bbs-tghs/uC-Uebungssystem-AVR/Bilder/20190724_152038.jpg

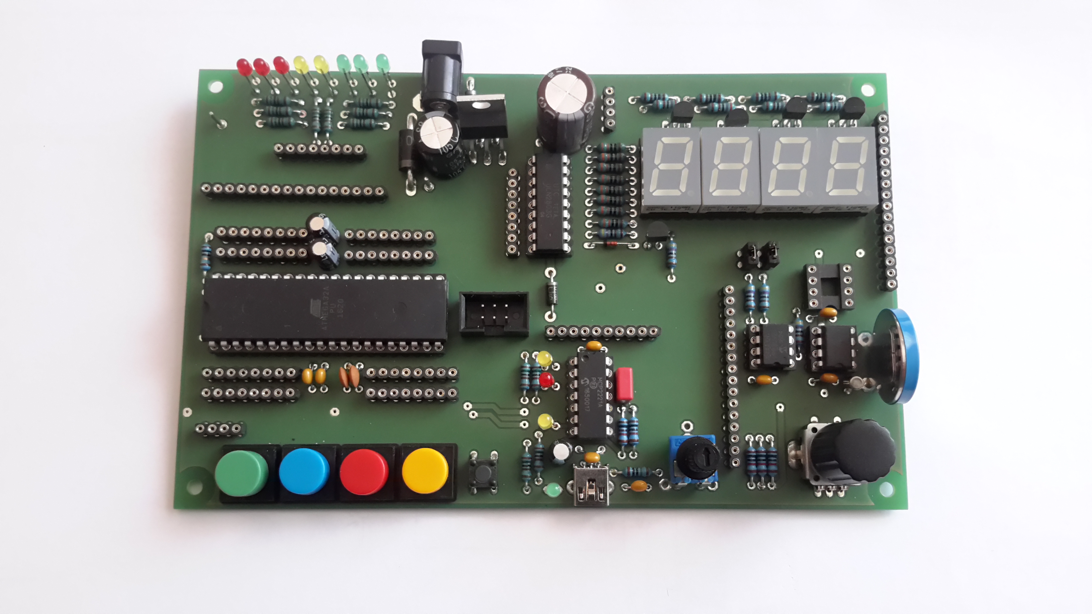
Bilder/20190724_152038.jpg
