bbs-tghs/uC-Uebungssystem-AVR/Bilder/20190724_152043.jpg

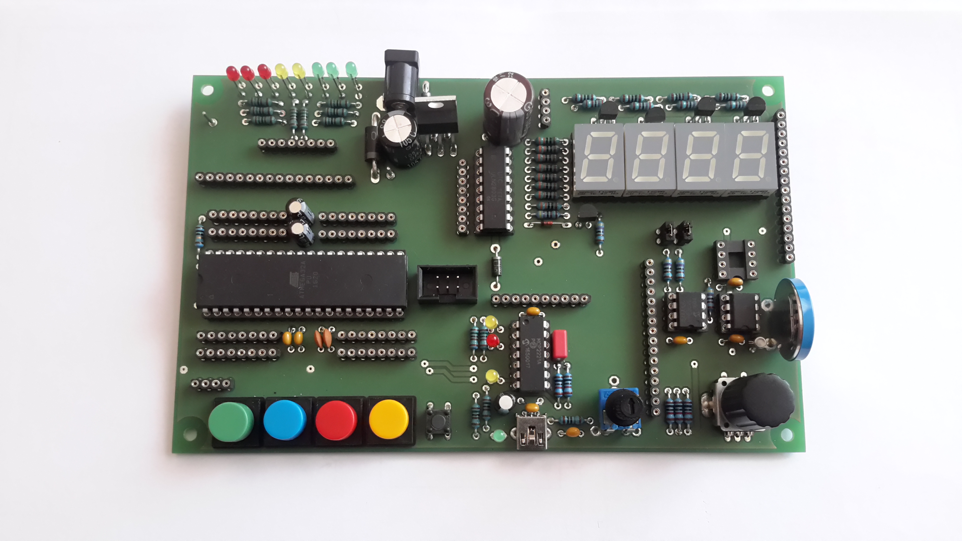
Bilder/20190724_152043.jpg
