bbs-tghs/uC-Uebungssystem-AVR/Bilder/20190724_152057.jpg

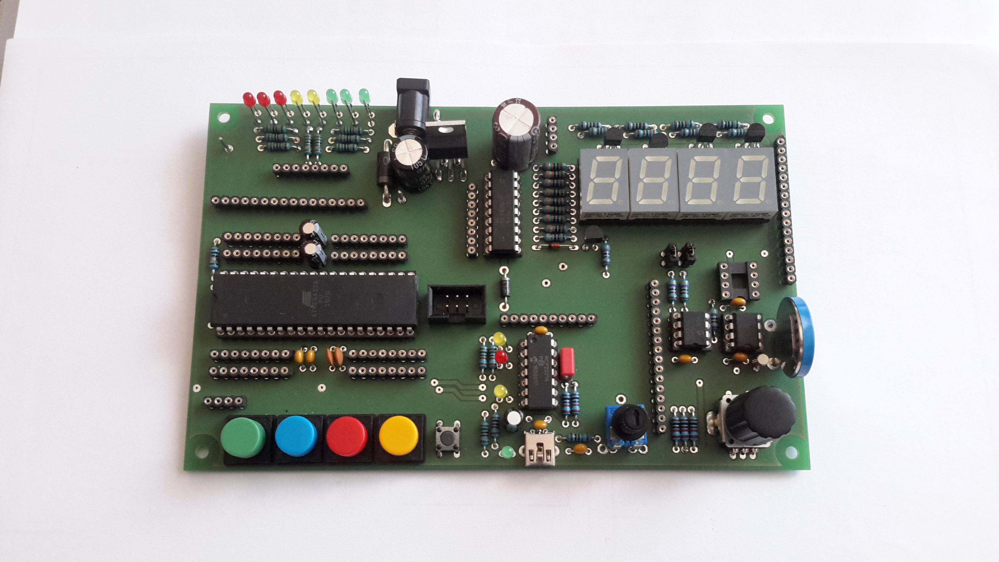
Bilder/20190724_152057.jpg
