bbs-tghs/uC-Uebungssystem-AVR/Bilder/BILD1885.JPG

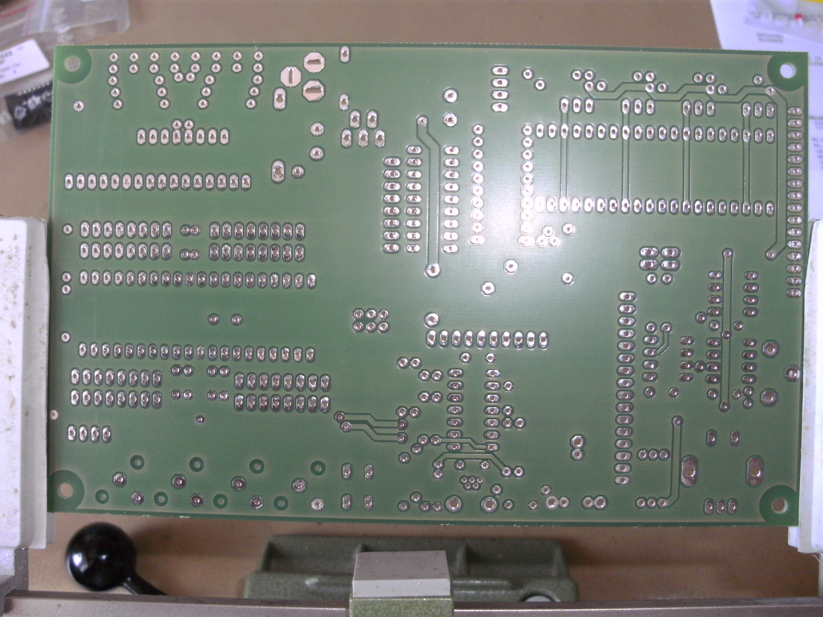
Bilder/BILD1885.JPG
