bbs-tghs/uC-Uebungssystem-AVR/Bilder/BILD1886.JPG

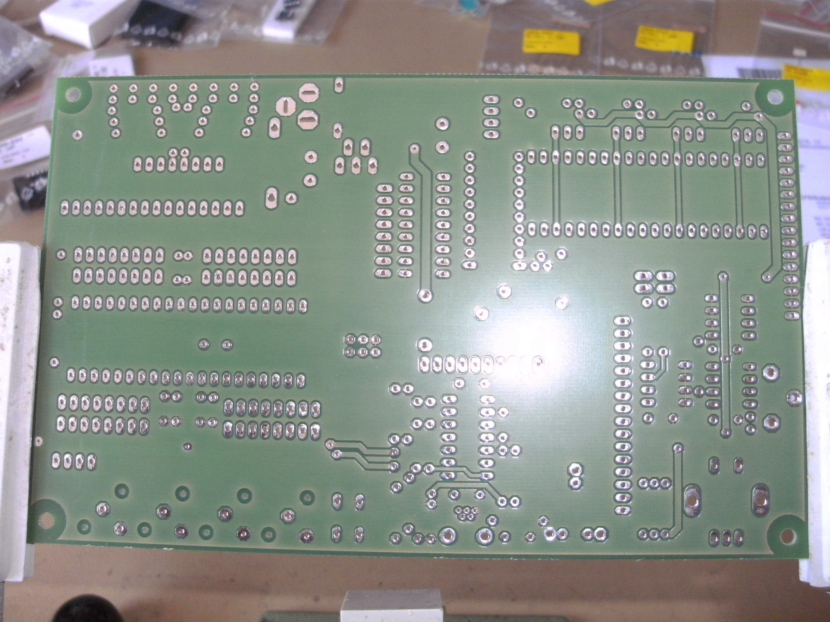
Bilder/BILD1886.JPG
