bbs-tghs/uC-Uebungssystem-AVR/Bilder/BILD1887.JPG

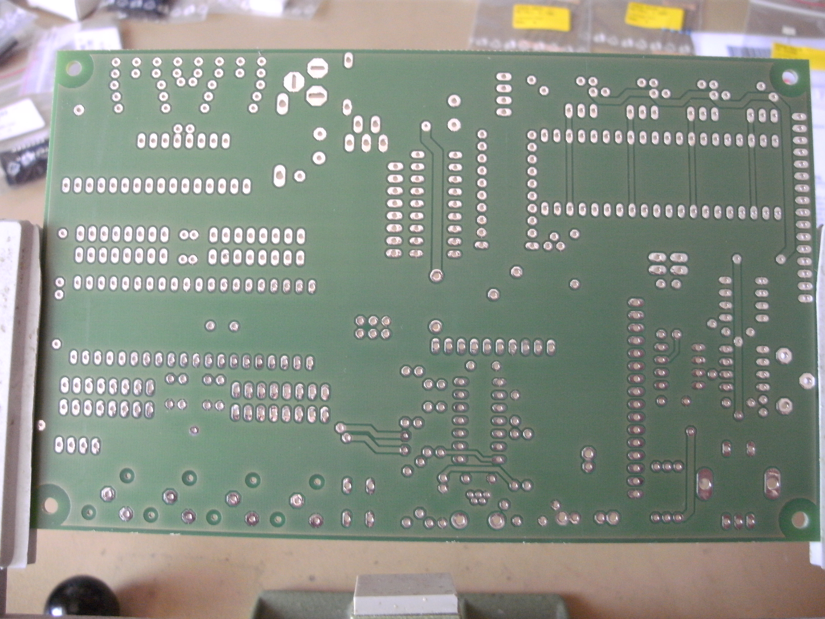
Bilder/BILD1887.JPG
