bbs-tghs/uC-Uebungssystem-AVR/Bilder/BILD1889.JPG

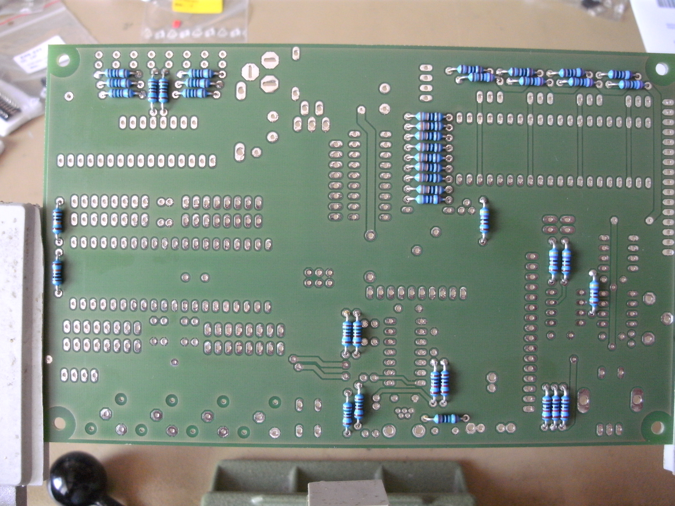
Bilder/BILD1889.JPG
