bbs-tghs/uC-Uebungssystem-AVR/Bilder/BILD1890.JPG

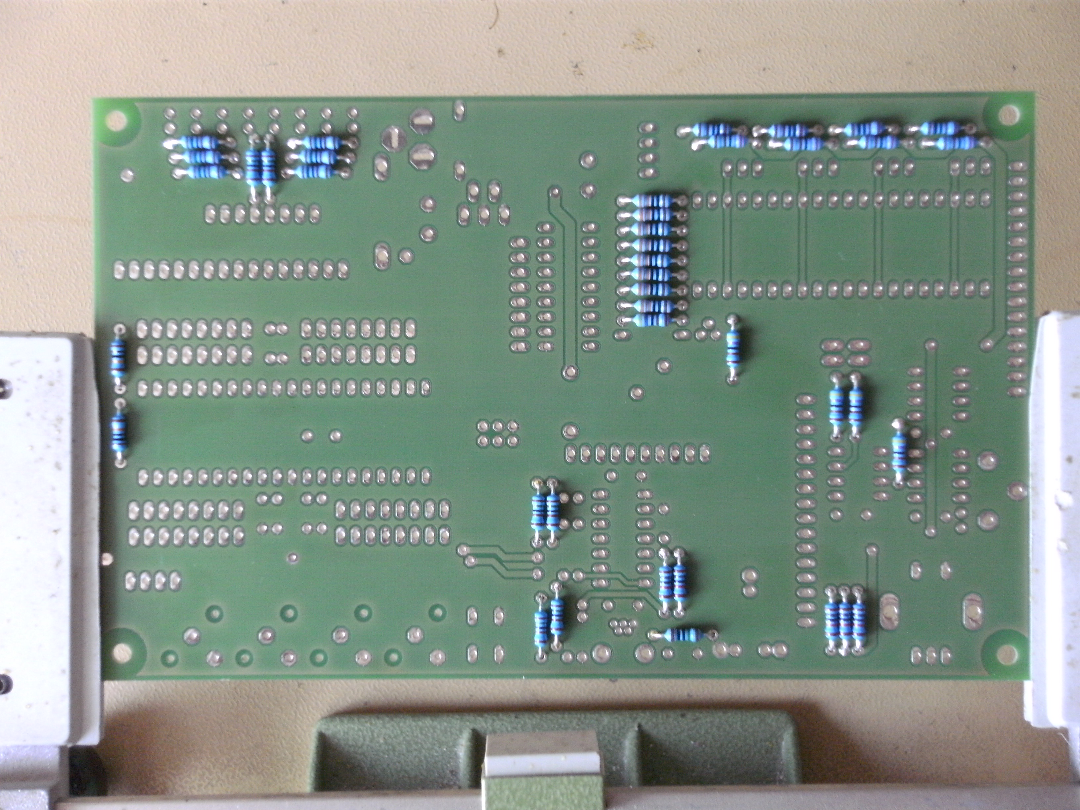
Bilder/BILD1890.JPG
