bbs-tghs/uC-Uebungssystem-AVR/Bilder/BILD1892.JPG

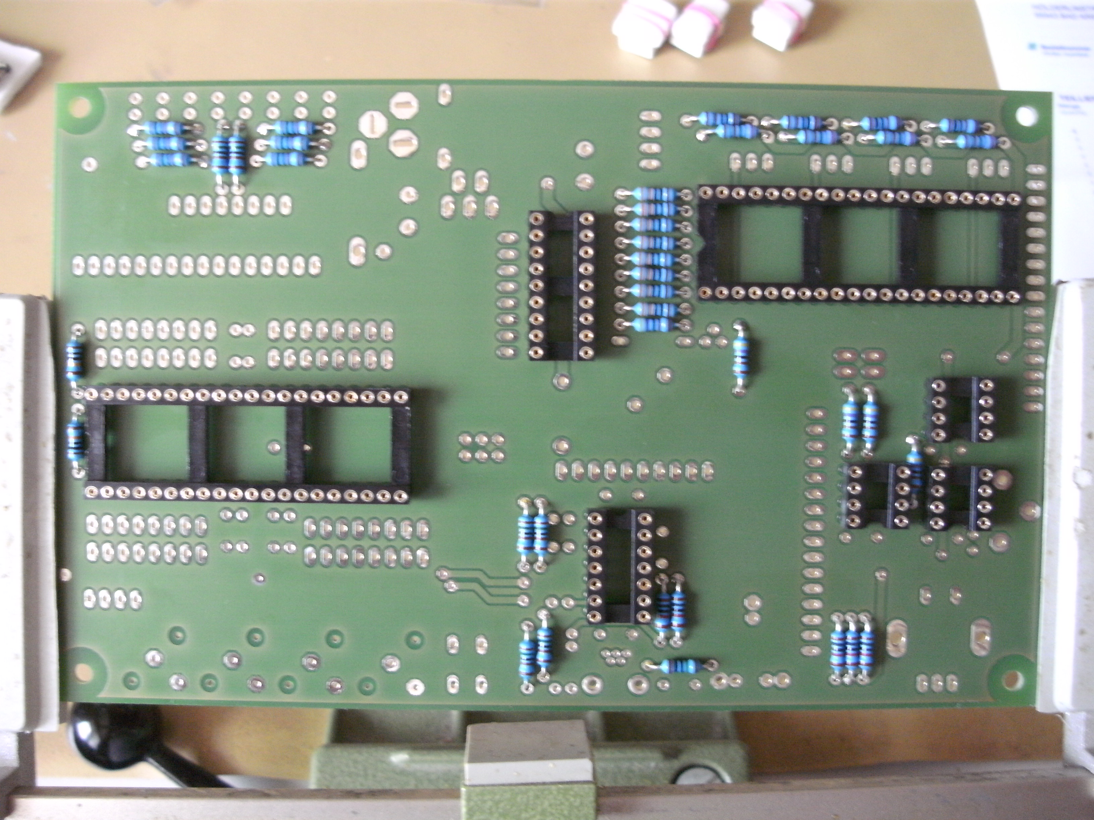
Bilder/BILD1892.JPG
