bbs-tghs/uC-Uebungssystem-AVR/Bilder/BILD1894.JPG

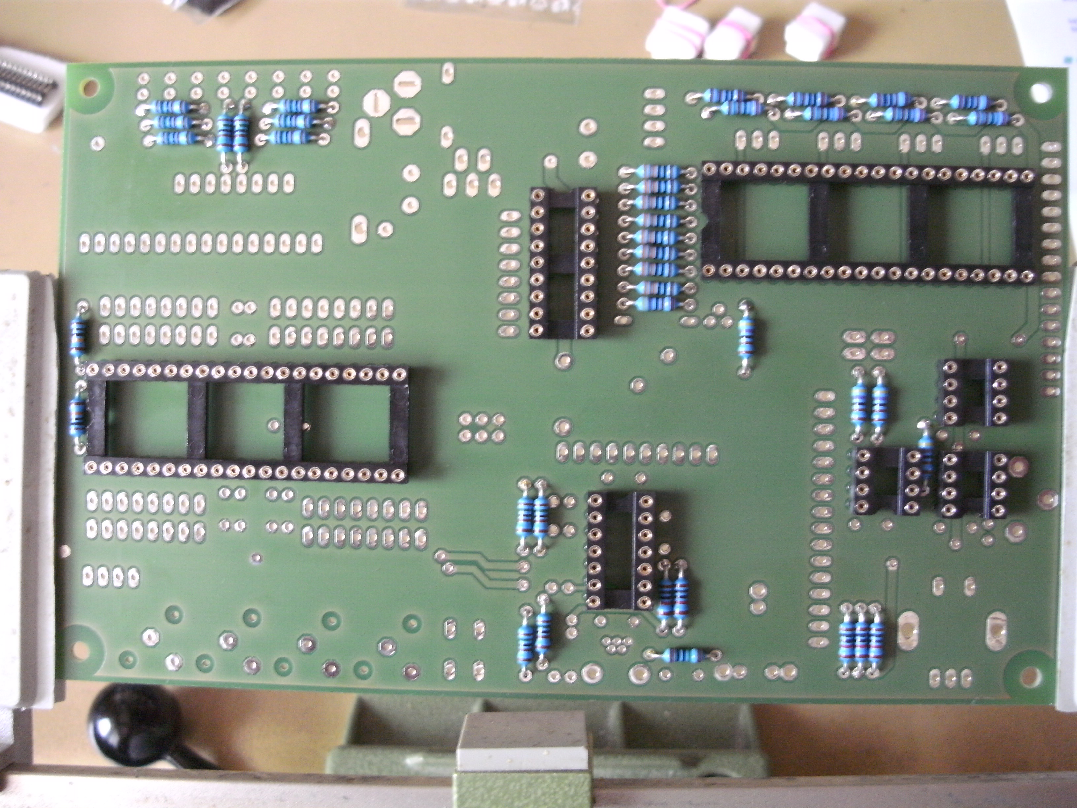
Bilder/BILD1894.JPG
