bbs-tghs/uC-Uebungssystem-AVR/Bilder/BILD1899.JPG

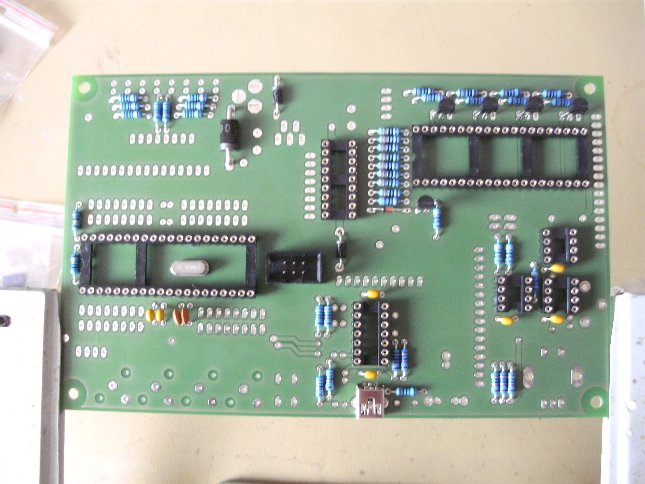
Bilder/BILD1899.JPG
