bbs-tghs/uC-Uebungssystem-AVR/Bilder/BILD1901.JPG

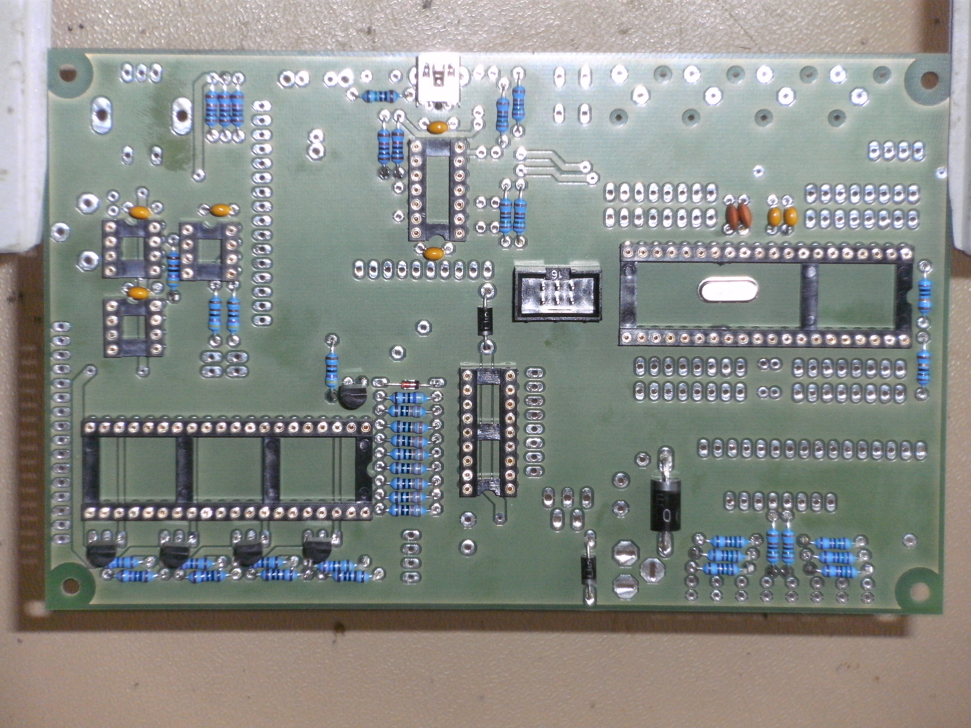
Bilder/BILD1901.JPG
