bbs-tghs/uC-Uebungssystem-AVR/Bilder/BILD1904.JPG

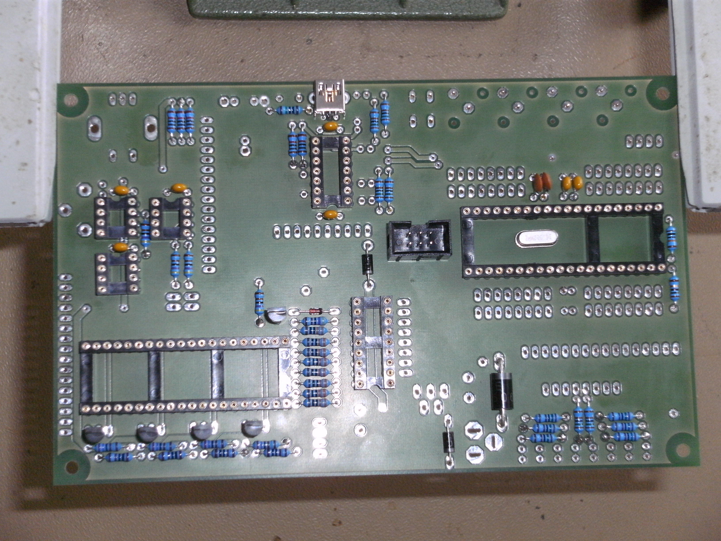
Bilder/BILD1904.JPG
