bbs-tghs/uC-Uebungssystem-AVR/Bilder/BILD1905.JPG

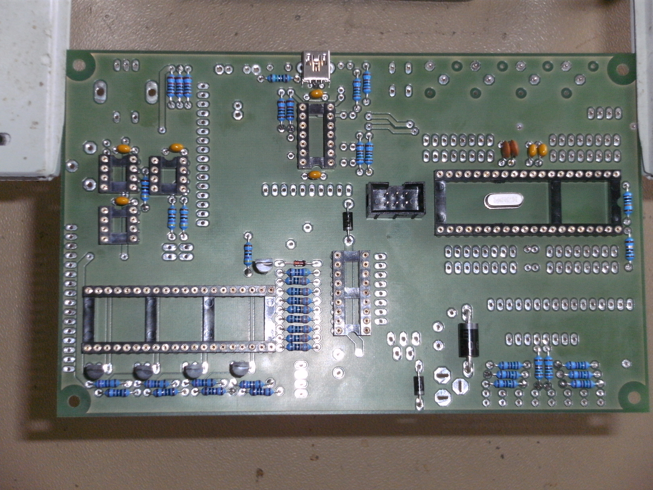
Bilder/BILD1905.JPG
