bbs-tghs/uC-Uebungssystem-AVR/Bilder/BILD1907.JPG

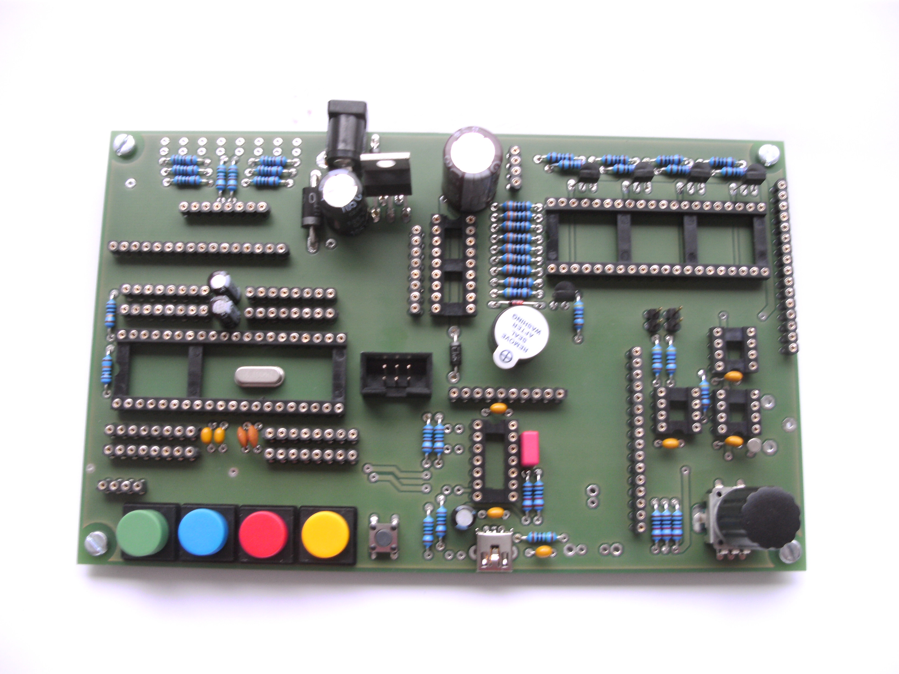
Bilder/BILD1907.JPG
