bbs-tghs/uC-Uebungssystem-AVR/Bilder/BILD1909.JPG

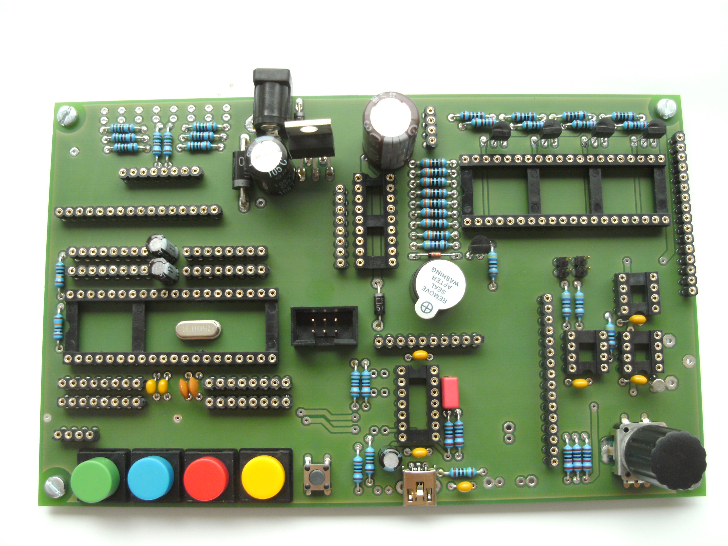
Bilder/BILD1909.JPG
