bbs-tghs/uC-Uebungssystem-AVR/Bilder/BILD1910.JPG

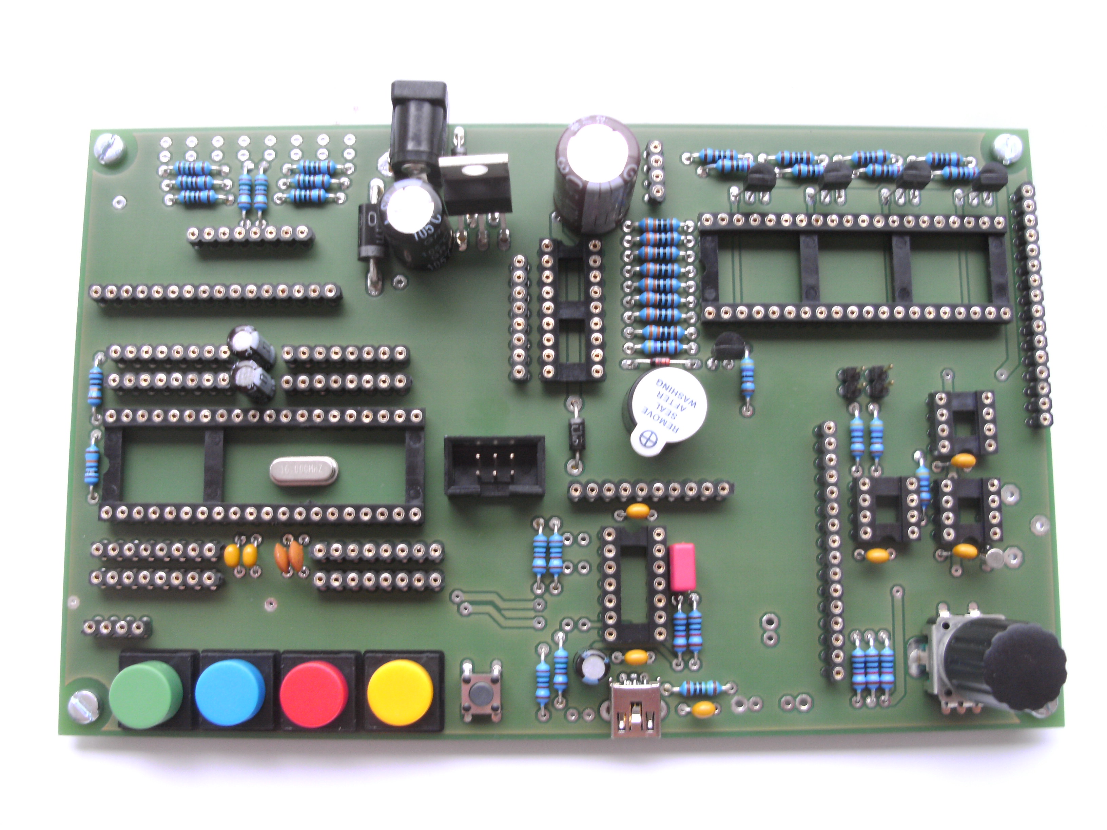
Bilder/BILD1910.JPG
