bbs-tghs/uC-Uebungssystem-AVR/Bilder/BILD1912.JPG

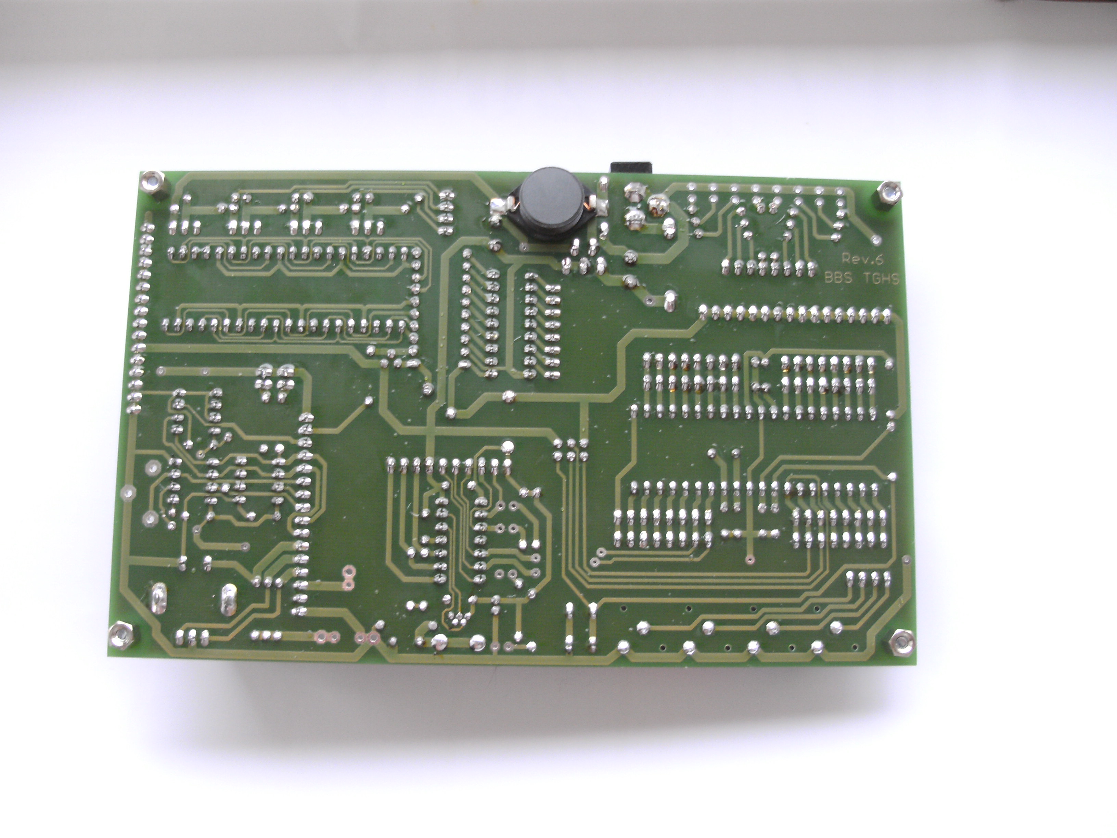
Bilder/BILD1912.JPG
