bbs-tghs/uC-Uebungssystem-AVR/Bilder/BILD1914.JPG

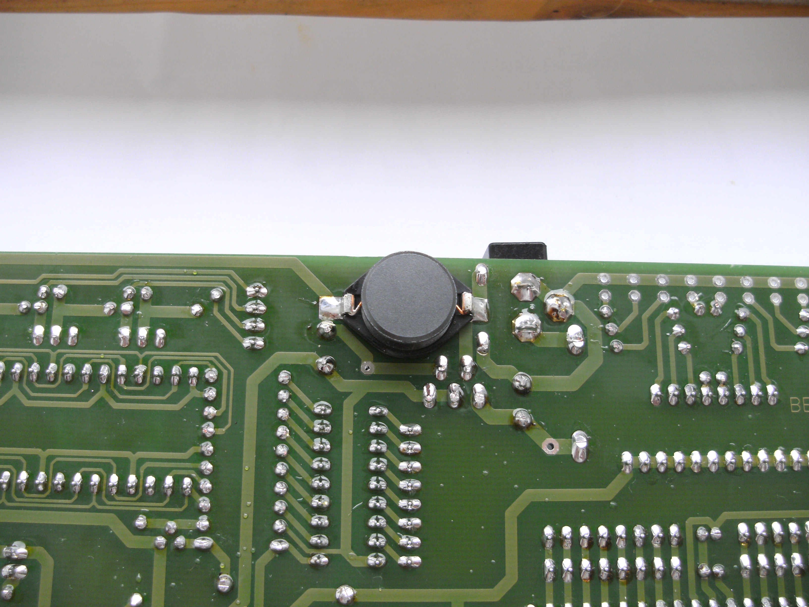
Bilder/BILD1914.JPG
