bbs-tghs/uC-Uebungssystem-AVR/Bilder/BILD1915.JPG

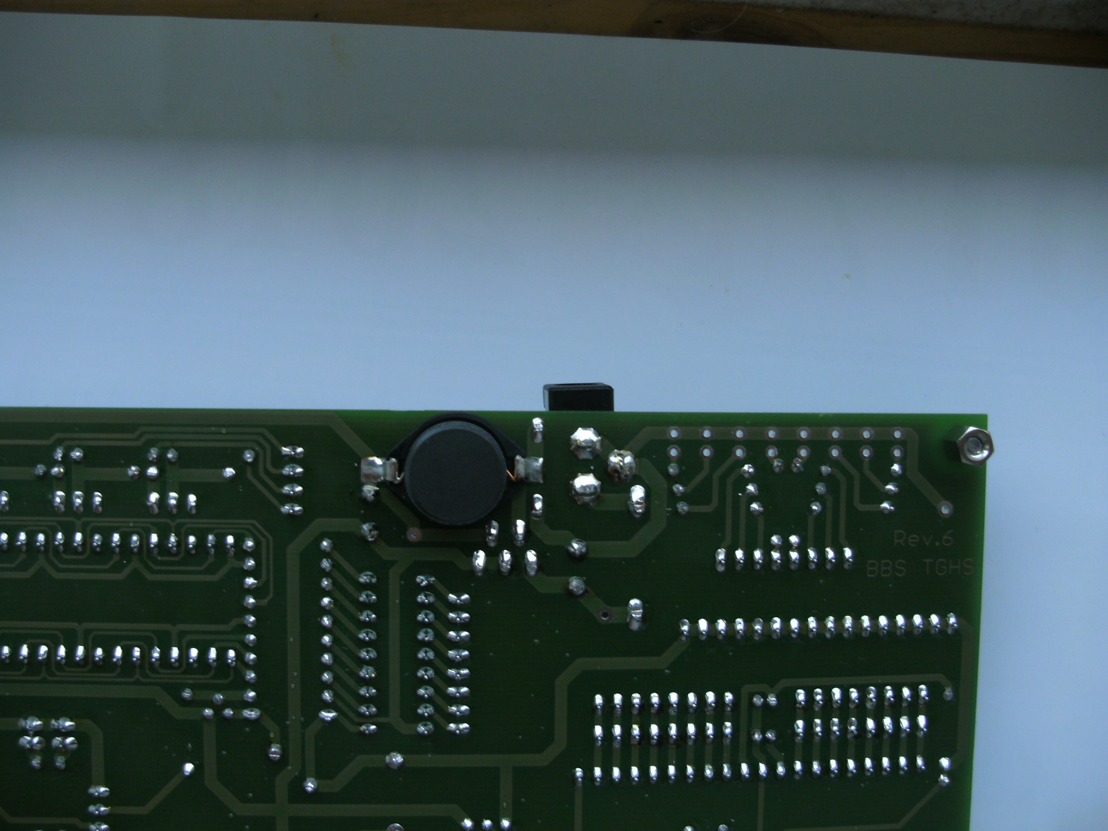
Bilder/BILD1915.JPG
