bbs-tghs/uC-Uebungssystem-AVR/Bilder/BILD1916.JPG

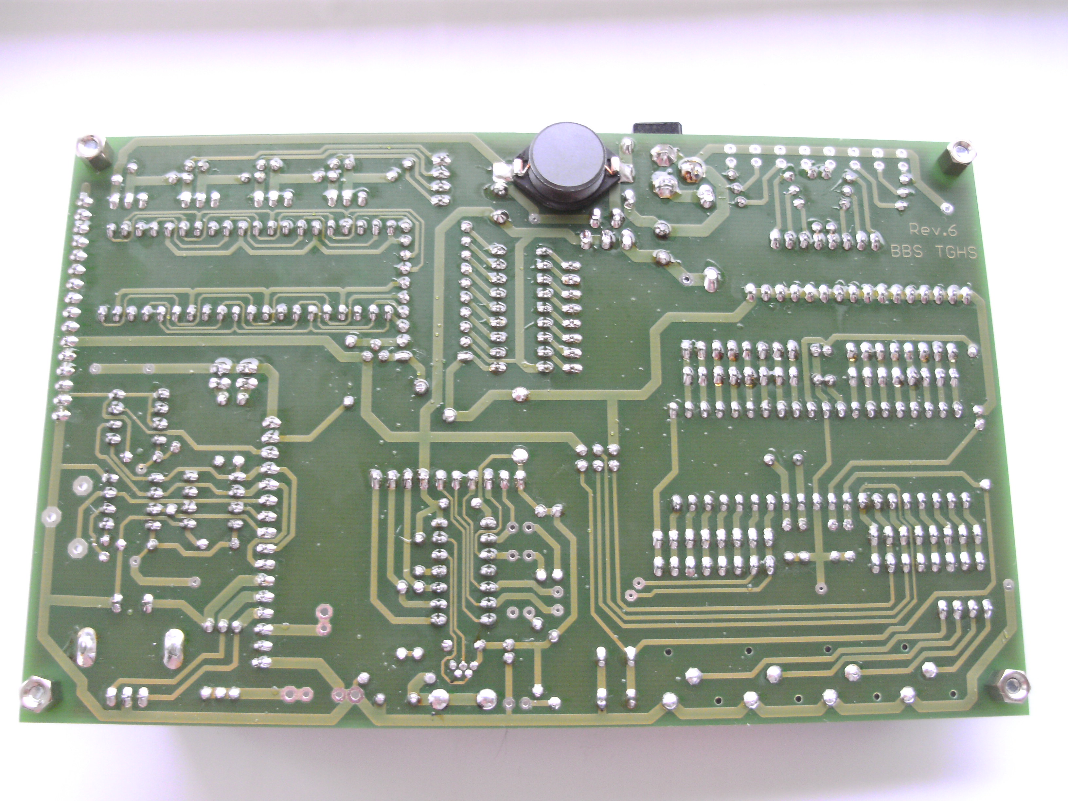
Bilder/BILD1916.JPG
