bbs-tghs/uC-Uebungssystem-AVR/Bilder/BILD1918.JPG

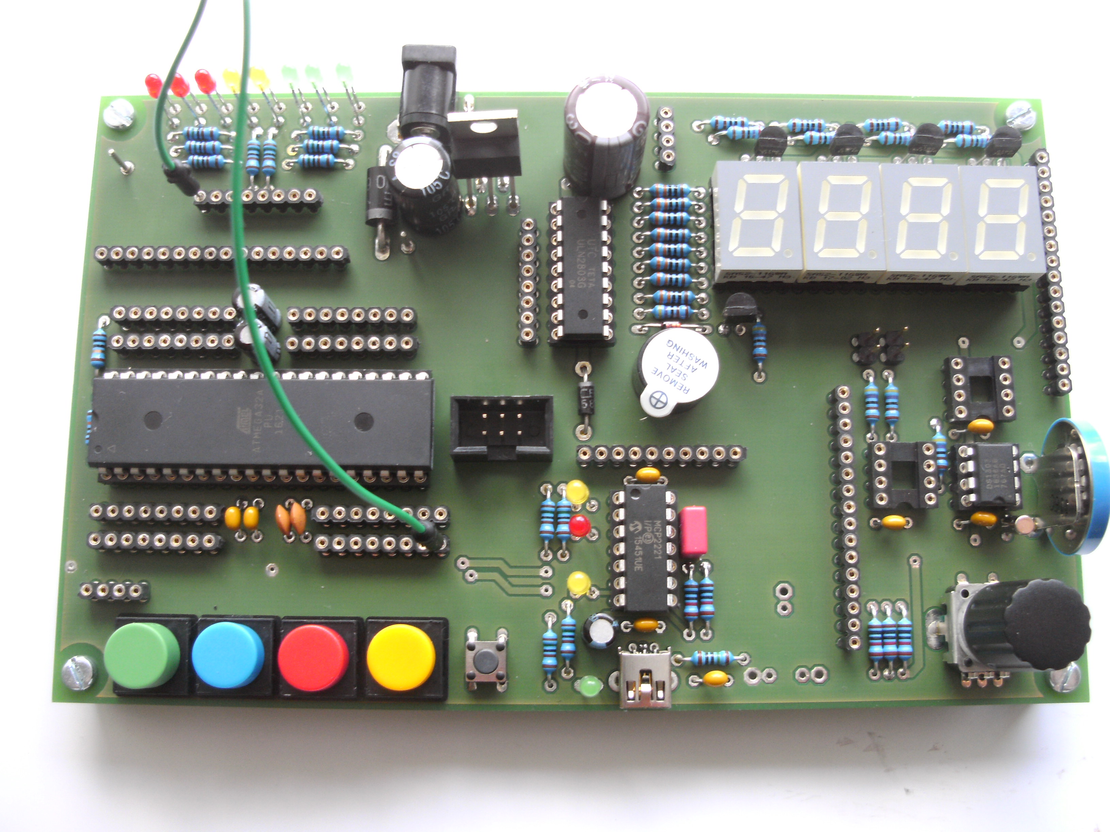
Bilder/BILD1918.JPG
