bbs-tghs/uC-Uebungssystem-AVR/Bilder/BILD1920.JPG

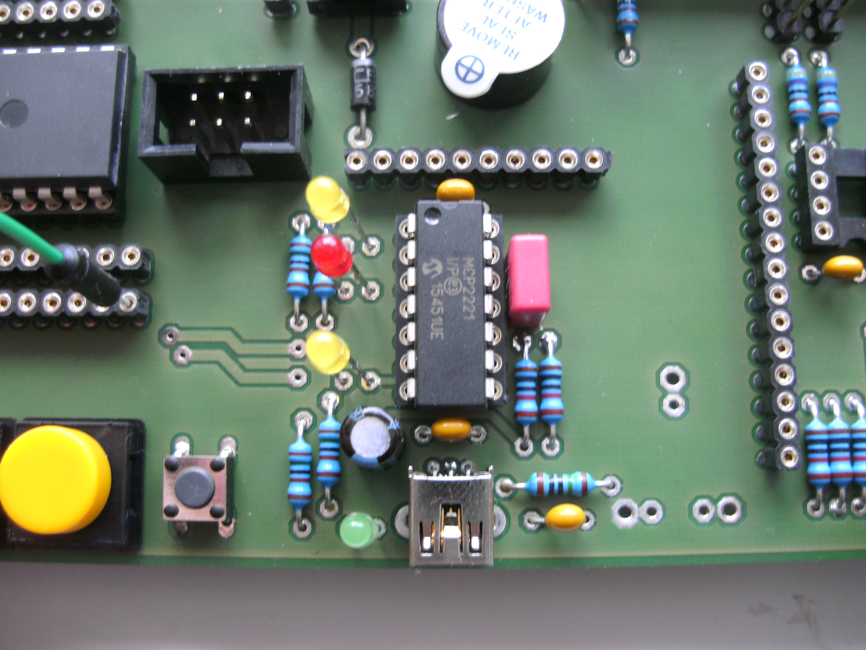
Bilder/BILD1920.JPG
