bbs-tghs/uC-Uebungssystem-AVR/Bilder/BILD1921.JPG

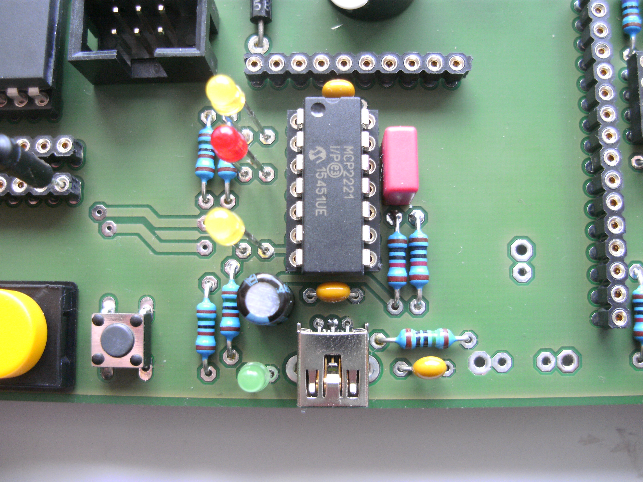
Bilder/BILD1921.JPG
