bbs-tghs/uC-Uebungssystem-AVR/Bilder/BILD1922.JPG

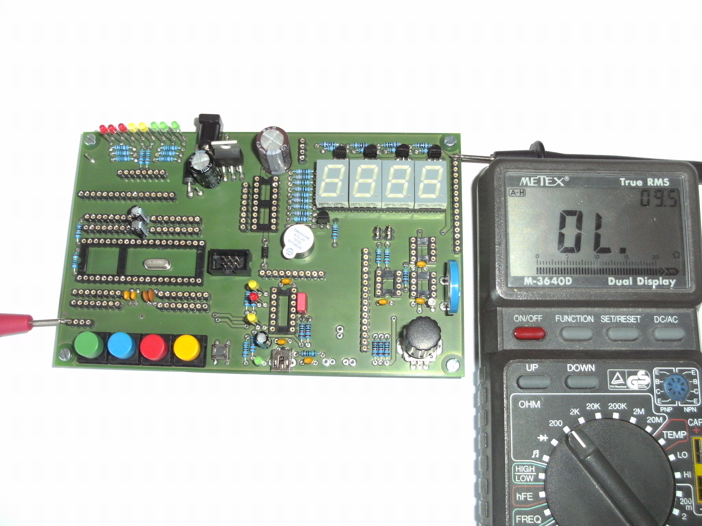
Bilder/BILD1922.JPG
