bbs-tghs/uC-Uebungssystem-AVR/Bilder/BILD1923.JPG

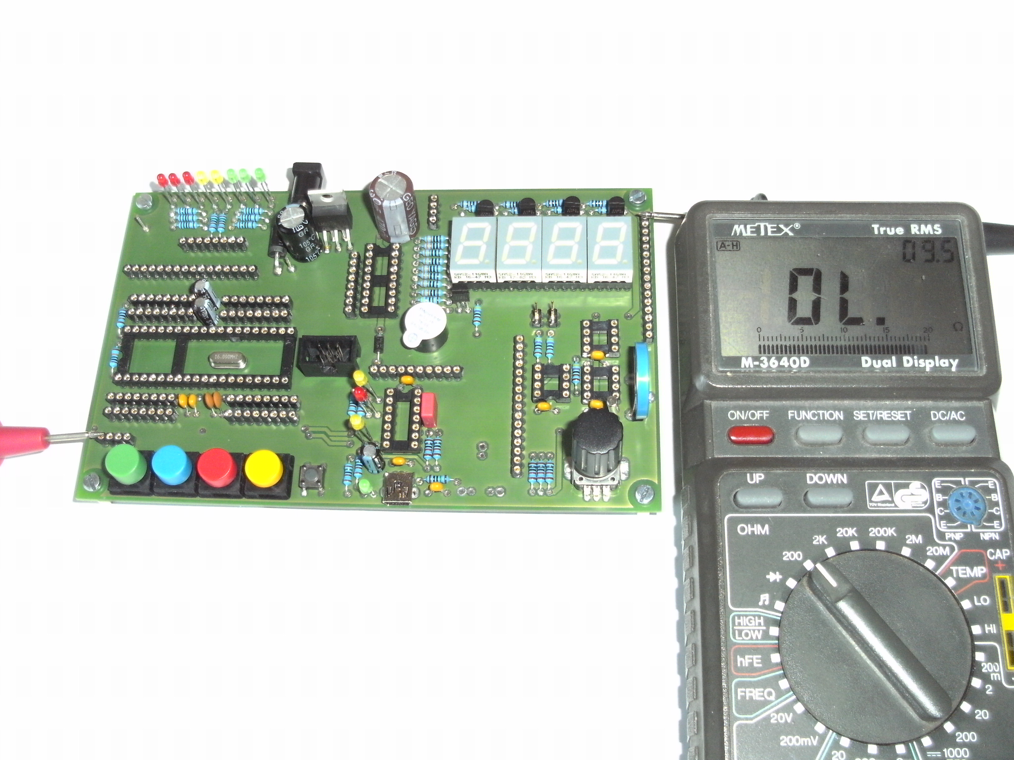
Bilder/BILD1923.JPG
