bbs-tghs/uC-Uebungssystem-AVR/Bilder/BILD1924.JPG

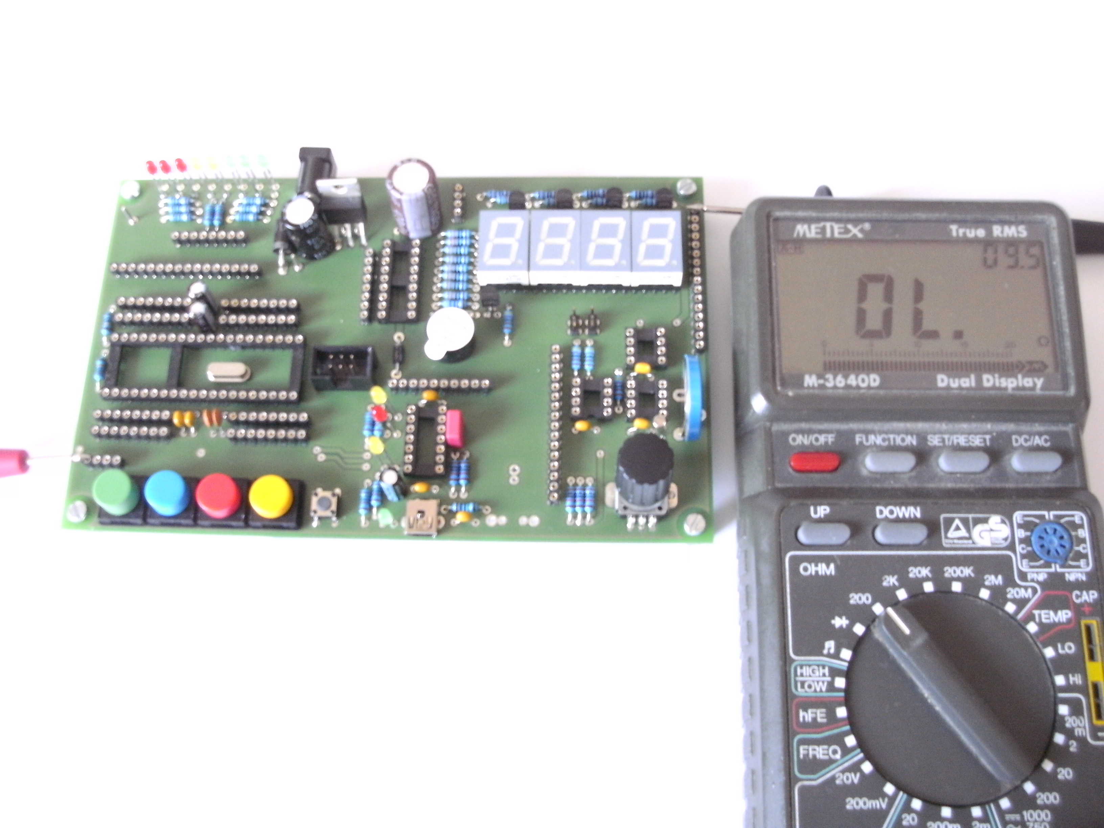
Bilder/BILD1924.JPG
