bbs-tghs/uC-Uebungssystem-AVR/Bilder/BILD1927.JPG

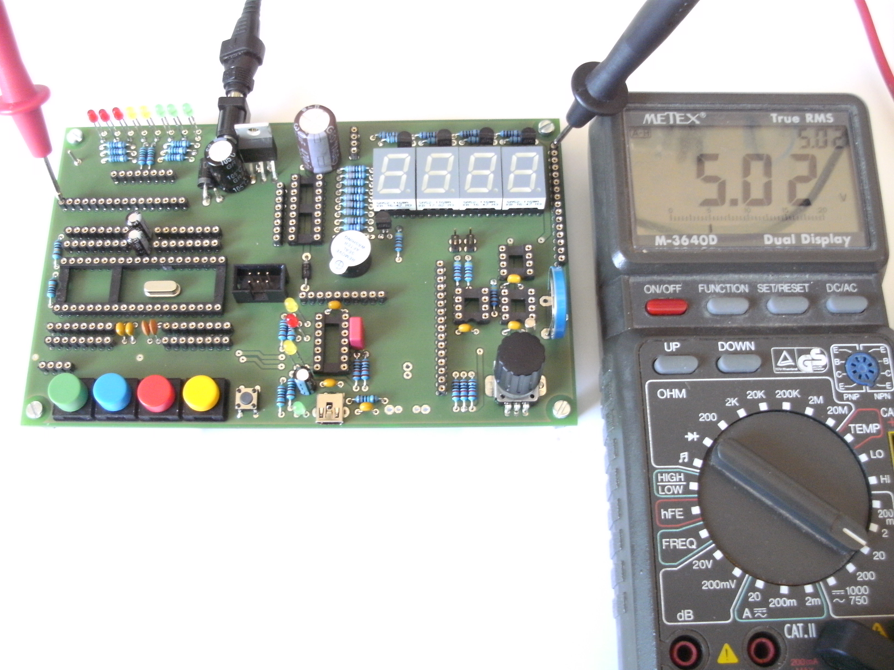
Bilder/BILD1927.JPG
