bbs-tghs/uC-Uebungssystem-AVR/Bilder/BILD1928.JPG

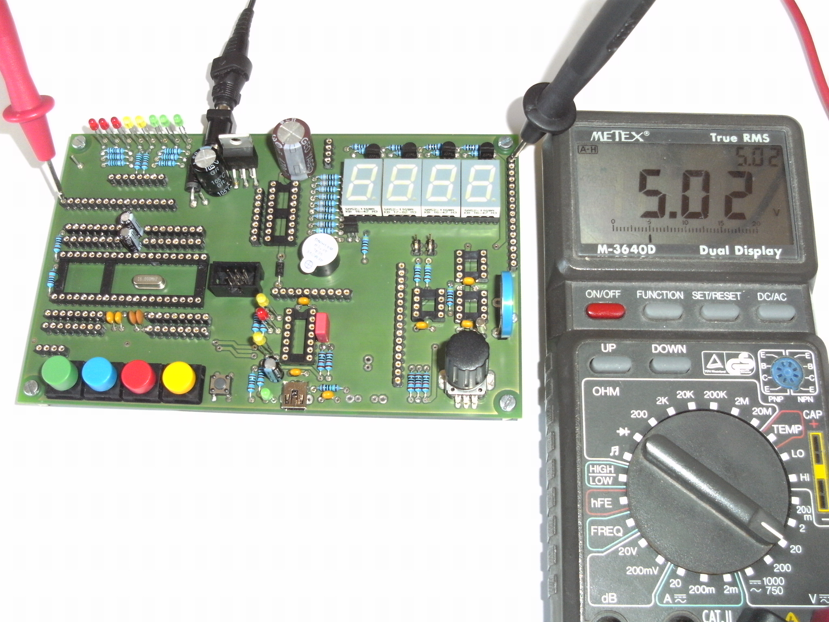
Bilder/BILD1928.JPG
