bbs-tghs/uC-Uebungssystem-AVR/Bilder/BILD1929.JPG

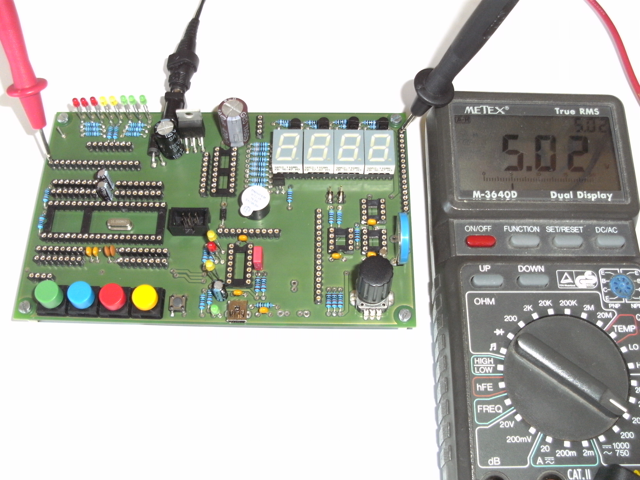
Bilder/BILD1929.JPG
