bbs-tghs/uC-Uebungssystem-AVR/Bilder/BILD1930.JPG

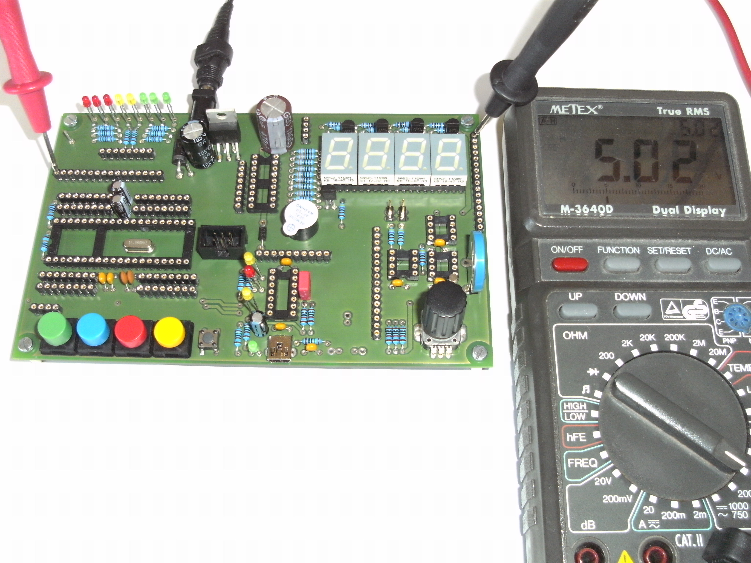
Bilder/BILD1930.JPG
