bbs-tghs/uC-Uebungssystem-AVR/Bilder/BILD1932.JPG

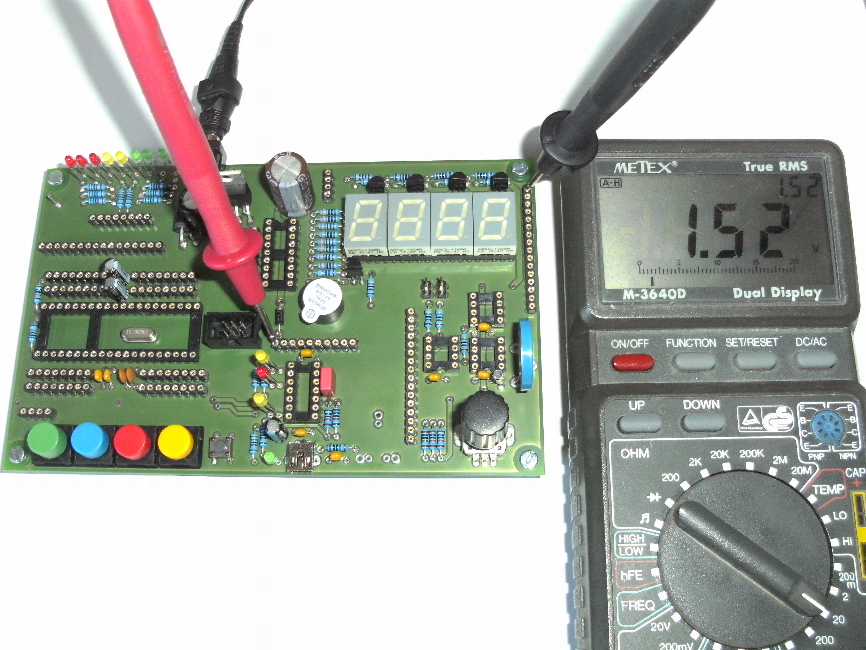
Bilder/BILD1932.JPG
