bbs-tghs/uC-Uebungssystem-AVR/Bilder/BILD1935.JPG

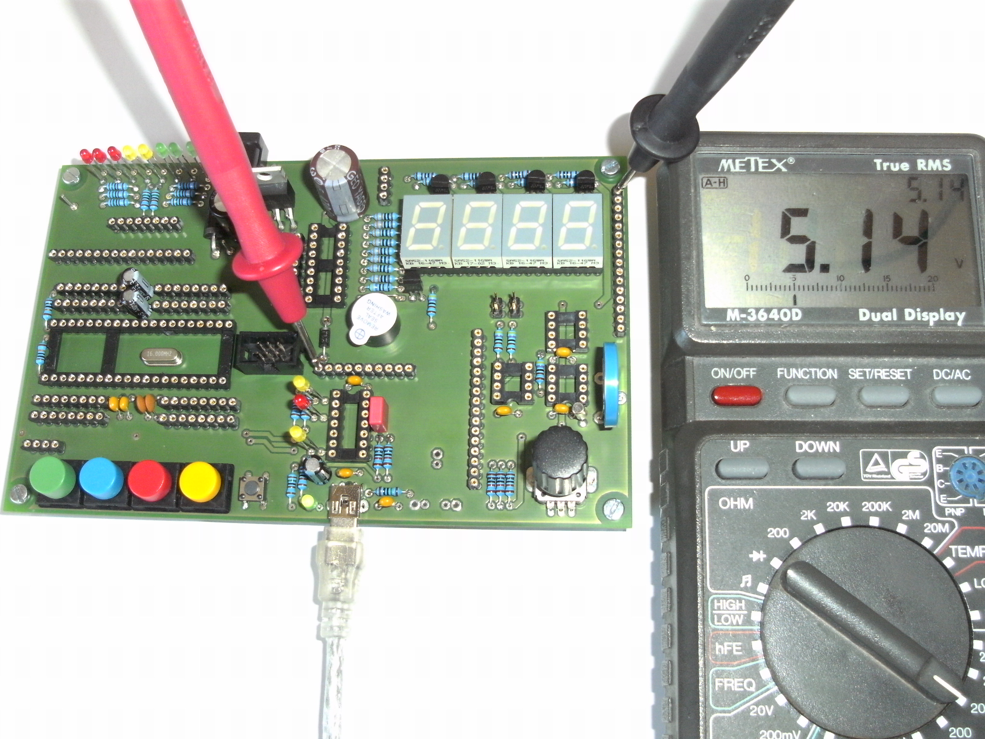
Bilder/BILD1935.JPG
