bbs-tghs/uC-Uebungssystem-AVR/Patch_1/20180627_170225.jpg

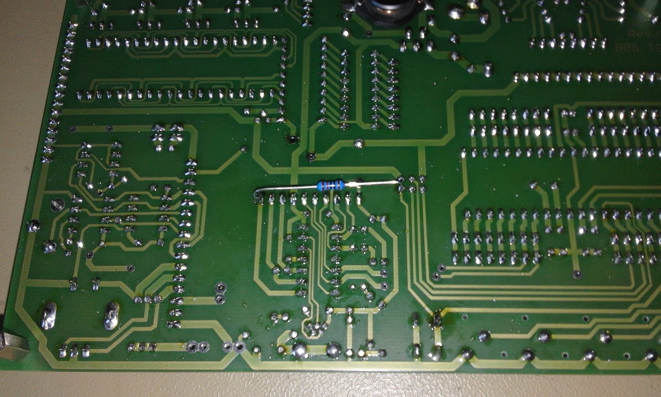
Patch_1/20180627_170225.jpg
