bbs-tghs/uC-Uebungssystem-AVR/Patch_1/20180627_170230.jpg

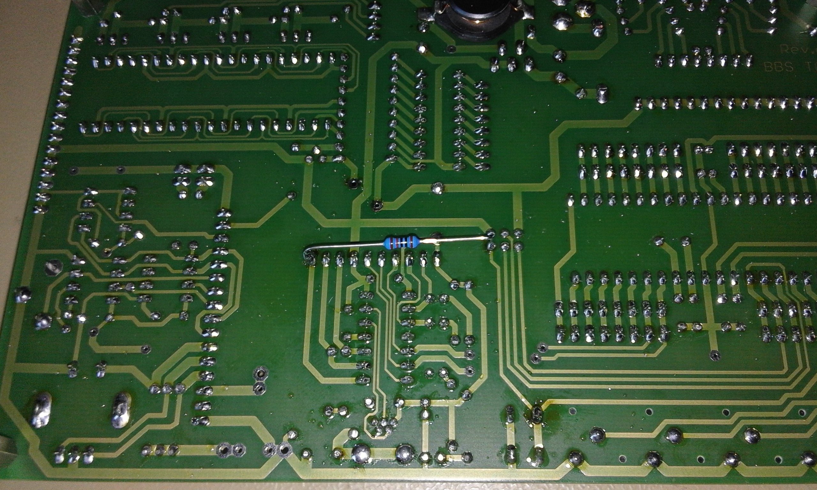
Patch_1/20180627_170230.jpg
